PatternAgents/ERA/revisions/Backplane_Reference_R2_0/images/Backplane_Reference_R1_0_top.png

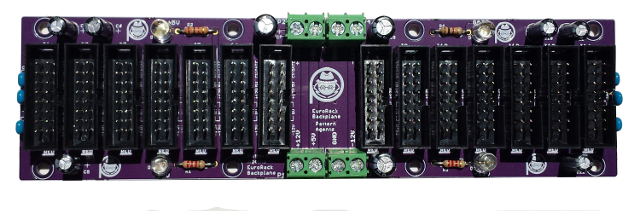
revisions/Backplane_Reference_R2_0/images/Backplane_Reference_R1_0_top.png
