PatternAgents/ERA/revisions/Backplane_Reference_R2_0/images/Backplane_Reference_R2_0_bot.png

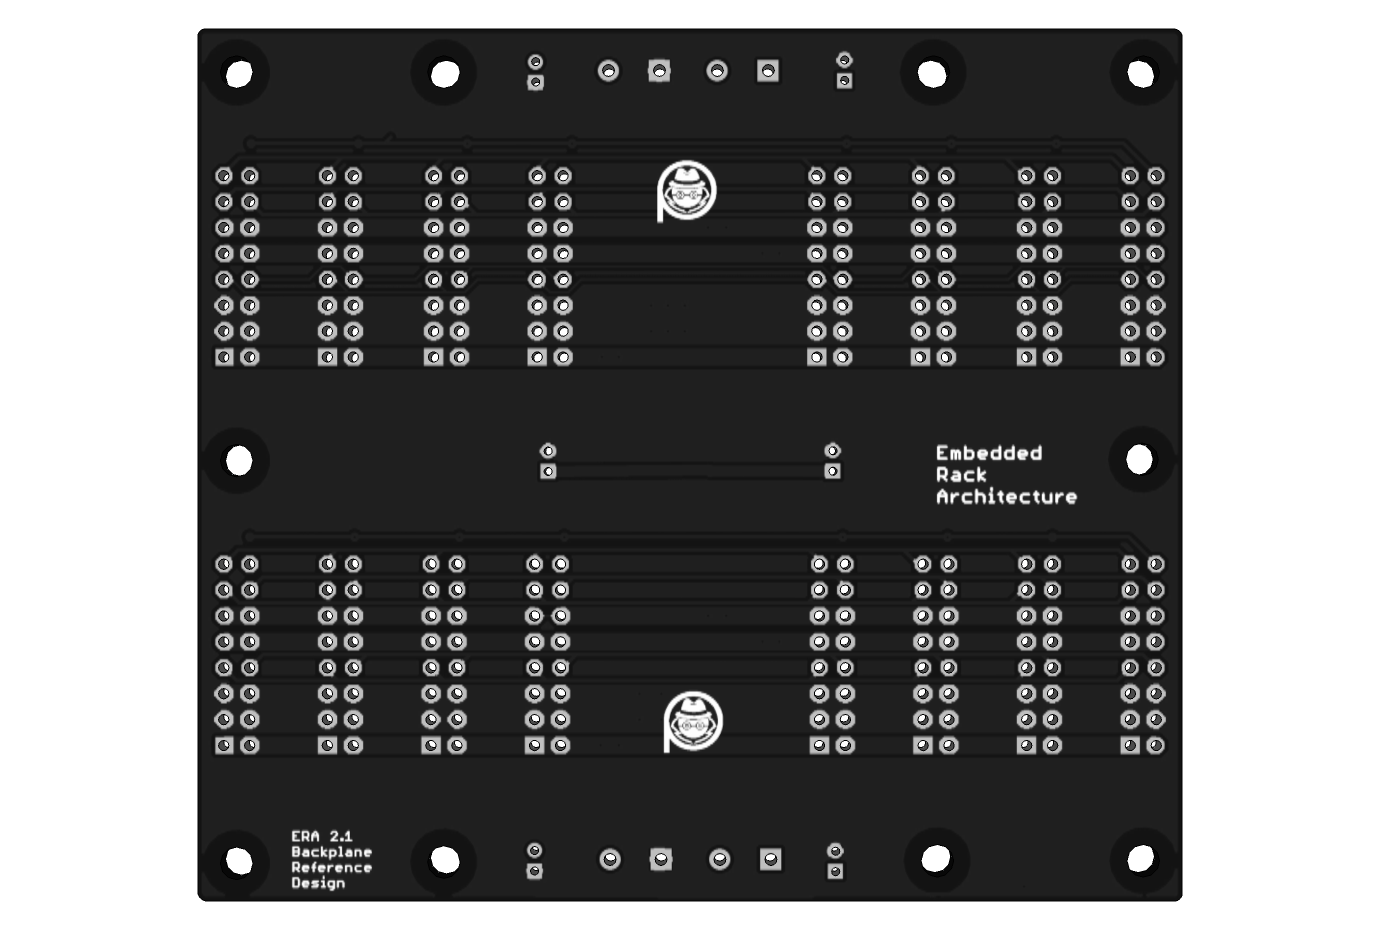
revisions/Backplane_Reference_R2_0/images/Backplane_Reference_R2_0_bot.png
