PatternAgents/ERA/revisions/Backplane_Reference_R2_0/images/Backplane_Reference_R2_0_iso.png

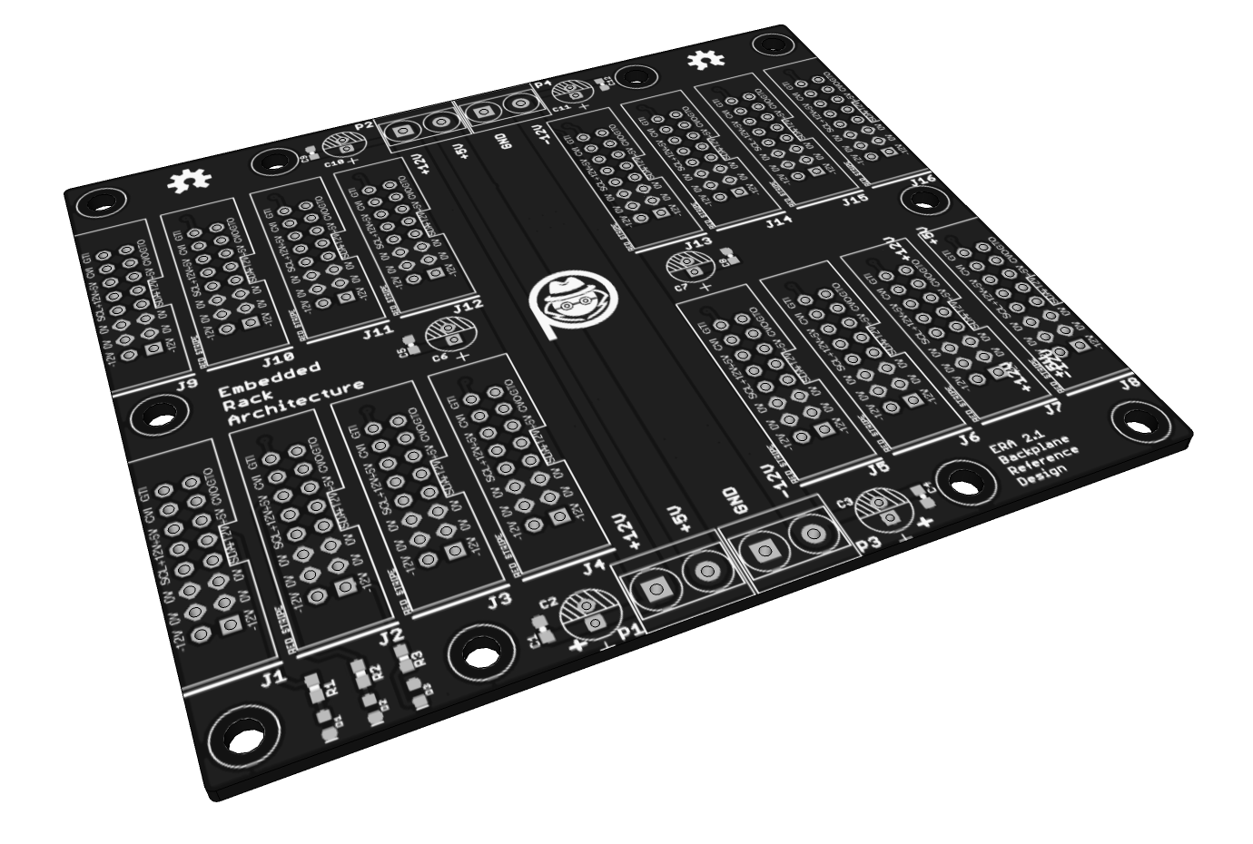
revisions/Backplane_Reference_R2_0/images/Backplane_Reference_R2_0_iso.png
