PatternAgents/ERA/revisions/Module_Templates_1U_PULP/examples/BAM/eagleUp/eagleUp_BAM_SIMPLE_1U_6HP_bottom_silk.png

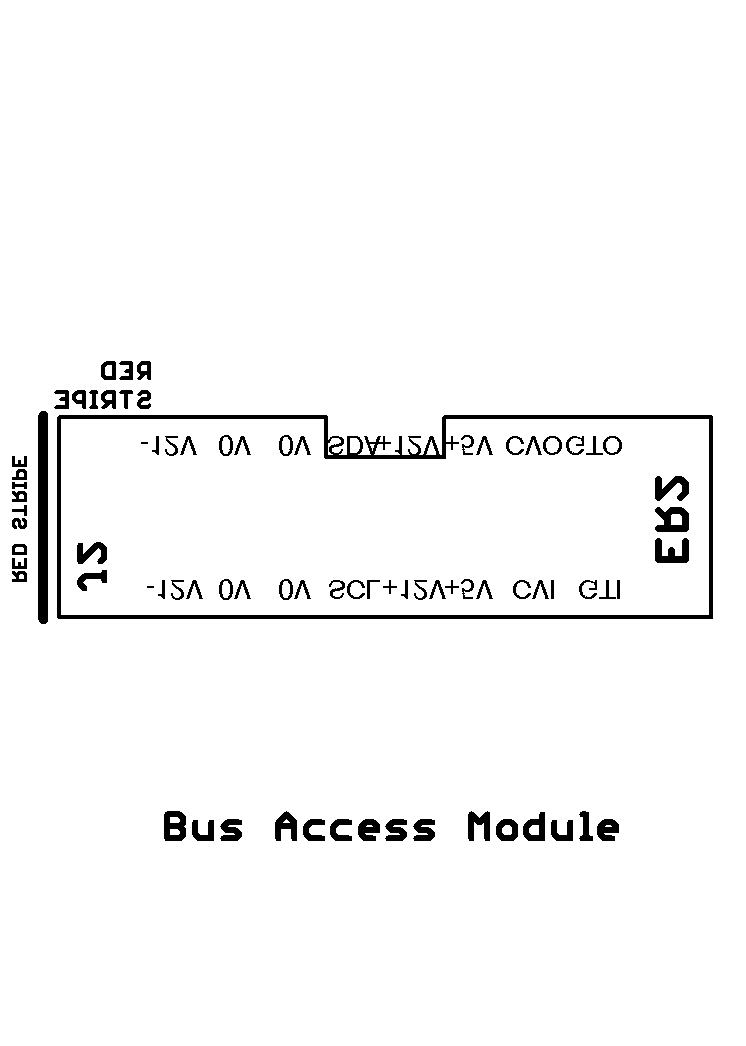
revisions/Module_Templates_1U_PULP/examples/BAM/eagleUp/eagleUp_BAM_SIMPLE_1U_6HP_bottom_silk.png
