PatternAgents/ERA/revisions/Module_Templates_1U_PULP/examples/BUF/eagleUp/eagleUp_BUF_1U_6HP_fpb_bottom.png

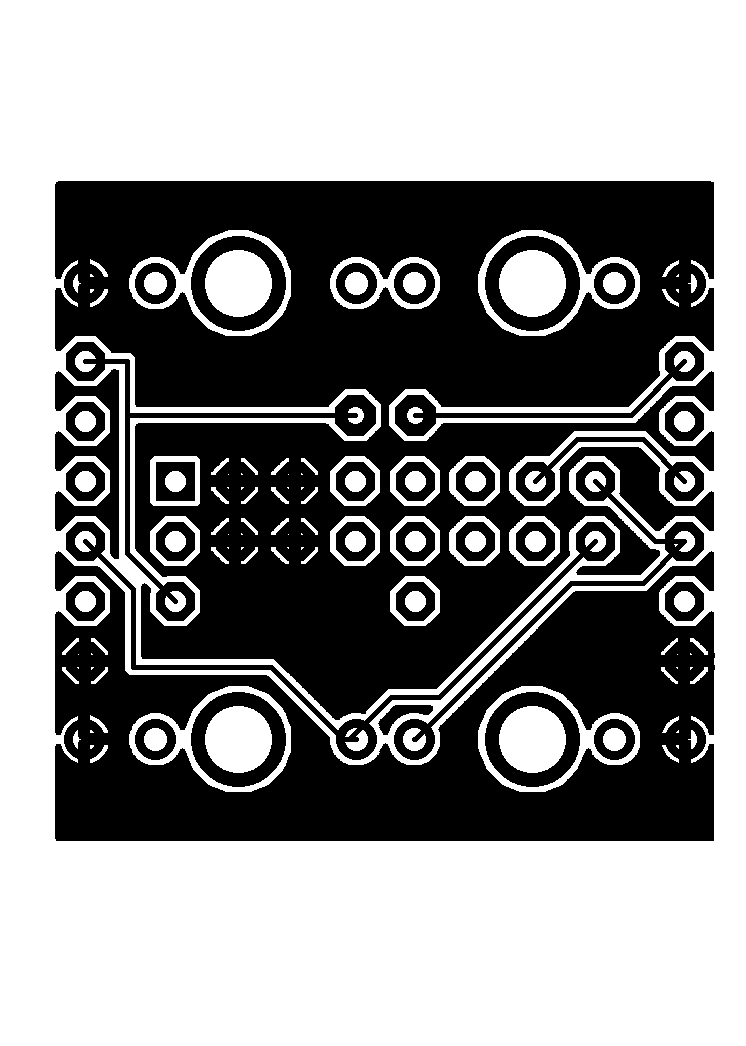
revisions/Module_Templates_1U_PULP/examples/BUF/eagleUp/eagleUp_BUF_1U_6HP_fpb_bottom.png
