PatternAgents/ERA/revisions/Module_Templates_1U_PULP/examples/BUF/eagleUp/eagleUp_BUF_1U_6HP_fpb_top.png

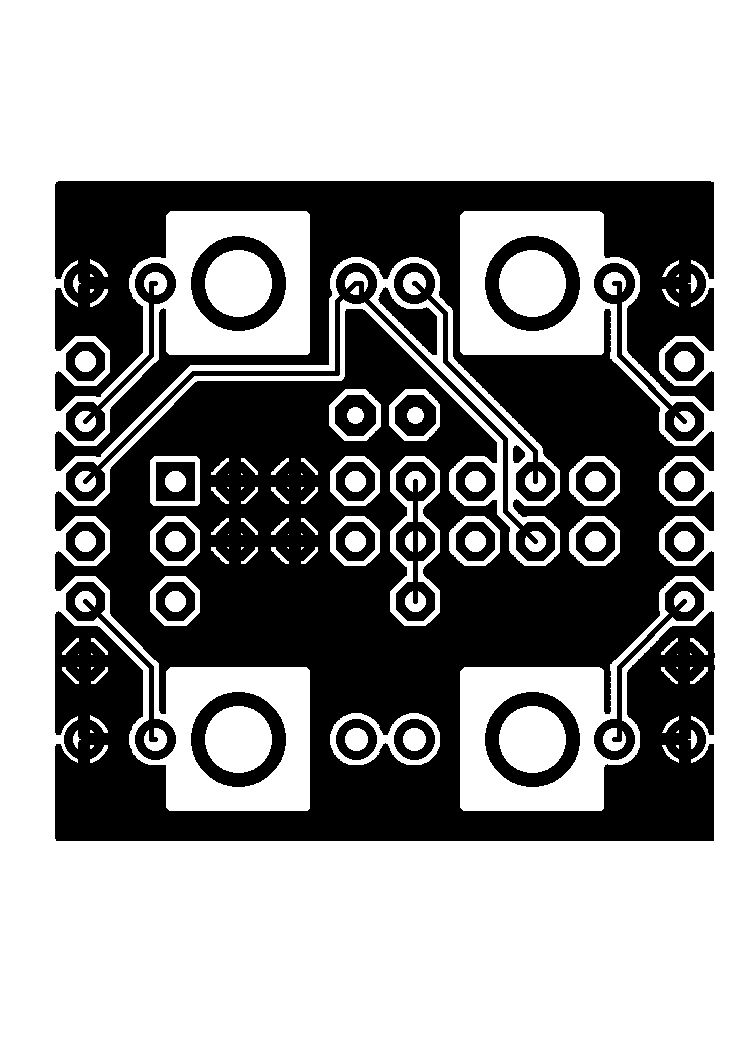
revisions/Module_Templates_1U_PULP/examples/BUF/eagleUp/eagleUp_BUF_1U_6HP_fpb_top.png
