PatternAgents/ERA/revisions/Module_Templates_3U/examples/BAM/eagleUp/eagleUp_BAM_Reference_R2_1_board_bottom.jpg

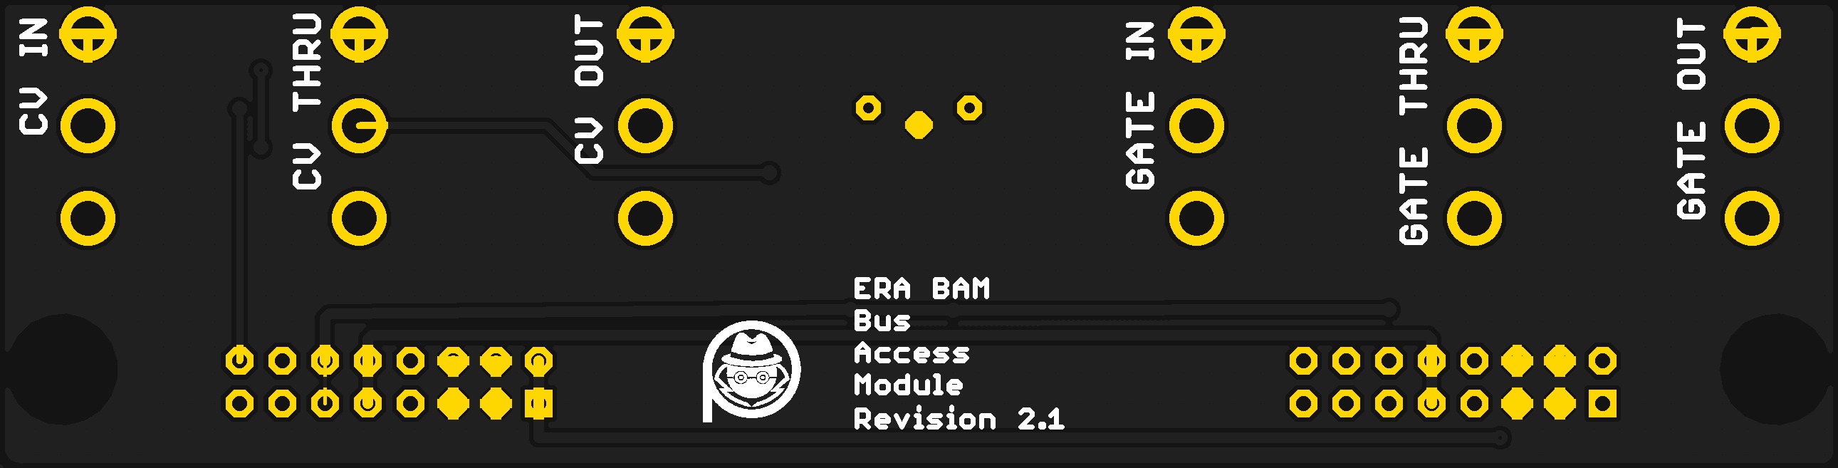
revisions/Module_Templates_3U/examples/BAM/eagleUp/eagleUp_BAM_Reference_R2_1_board_bottom.jpg
