PatternAgents/ERA/revisions/Module_Templates_3U/examples/BAM/images/BAM_iso.png

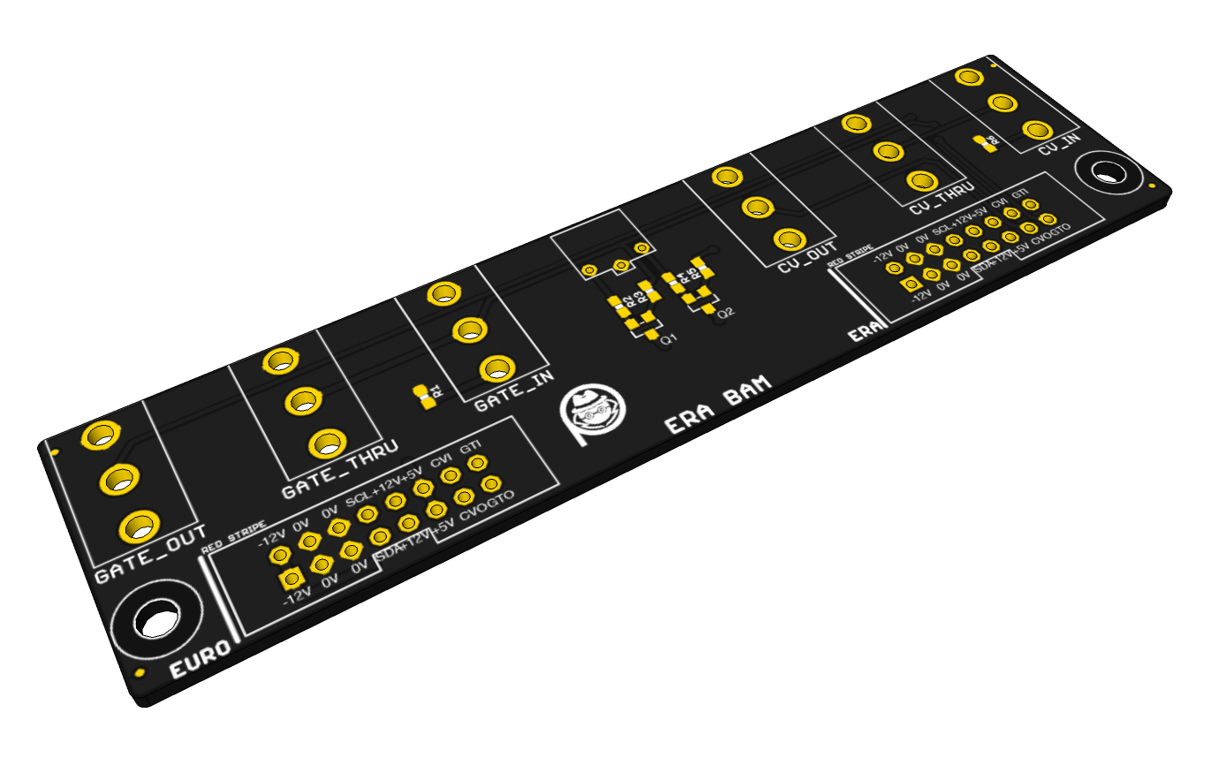
revisions/Module_Templates_3U/examples/BAM/images/BAM_iso.png
