PatternAgents/ERA/revisions/Module_Templates_3U/examples/midi_block/pcb/eagleUp/eagleUp_midi_block_board_bottom.jpg

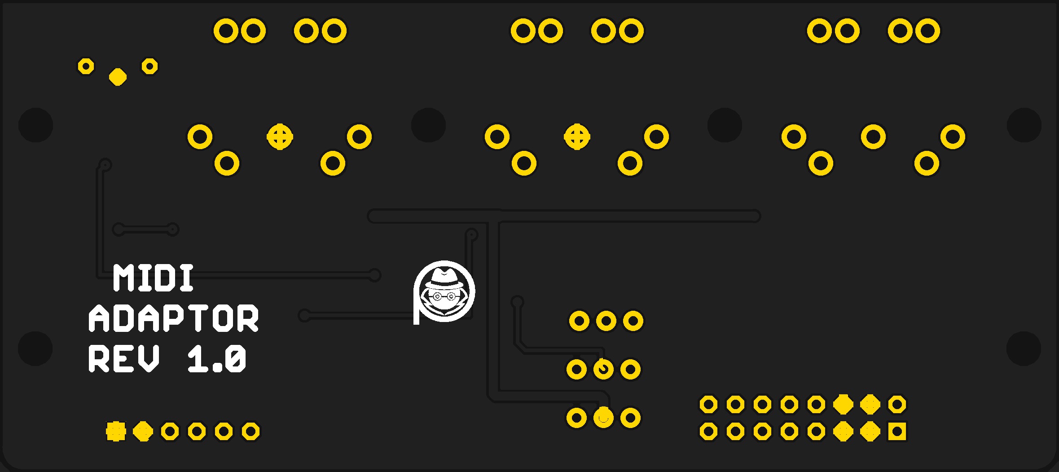
revisions/Module_Templates_3U/examples/midi_block/pcb/eagleUp/eagleUp_midi_block_board_bottom.jpg
