PatternAgents/ERA/revisions/Module_Templates_3U/examples/SwitchMult/eagleUp/eagleUp_SwitchMult_board_bottom.jpg

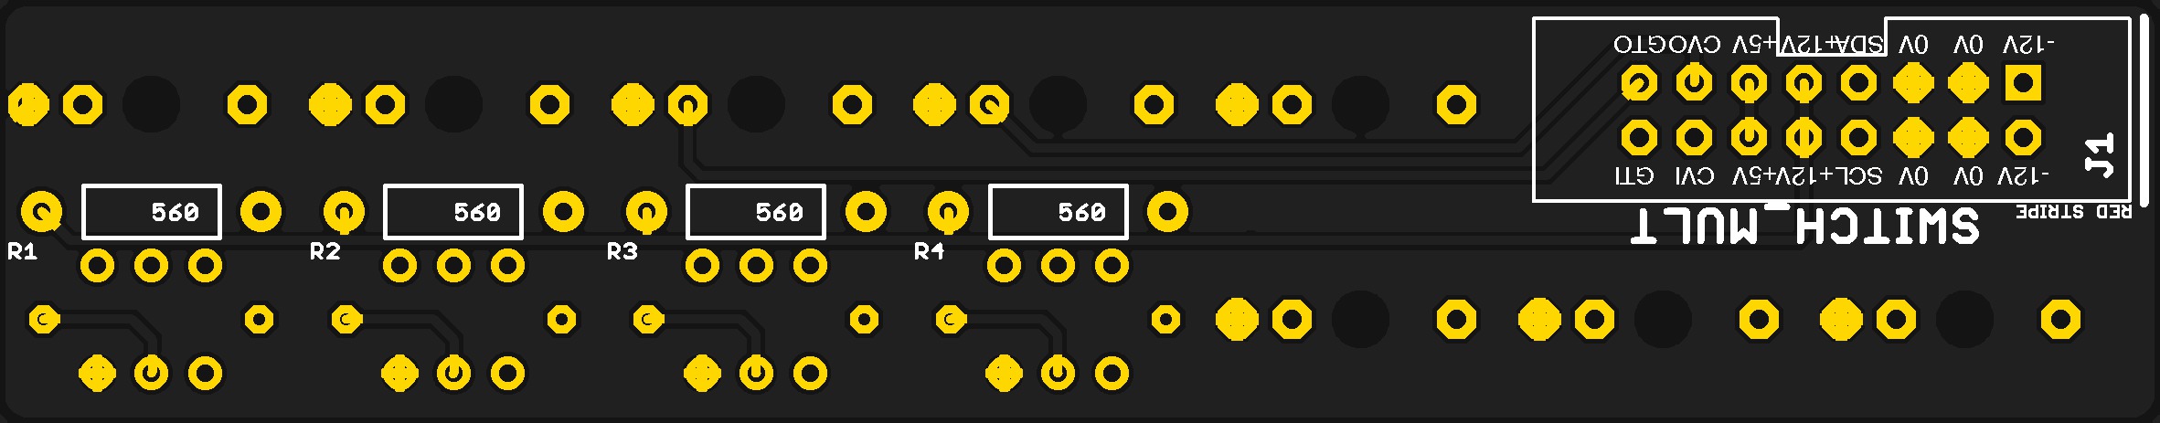
revisions/Module_Templates_3U/examples/SwitchMult/eagleUp/eagleUp_SwitchMult_board_bottom.jpg
