PatternAgents/ERA/revisions/Module_Templates_3U/examples/SwitchMult/eagleUp/eagleUp_SwitchMult_board_top.jpg

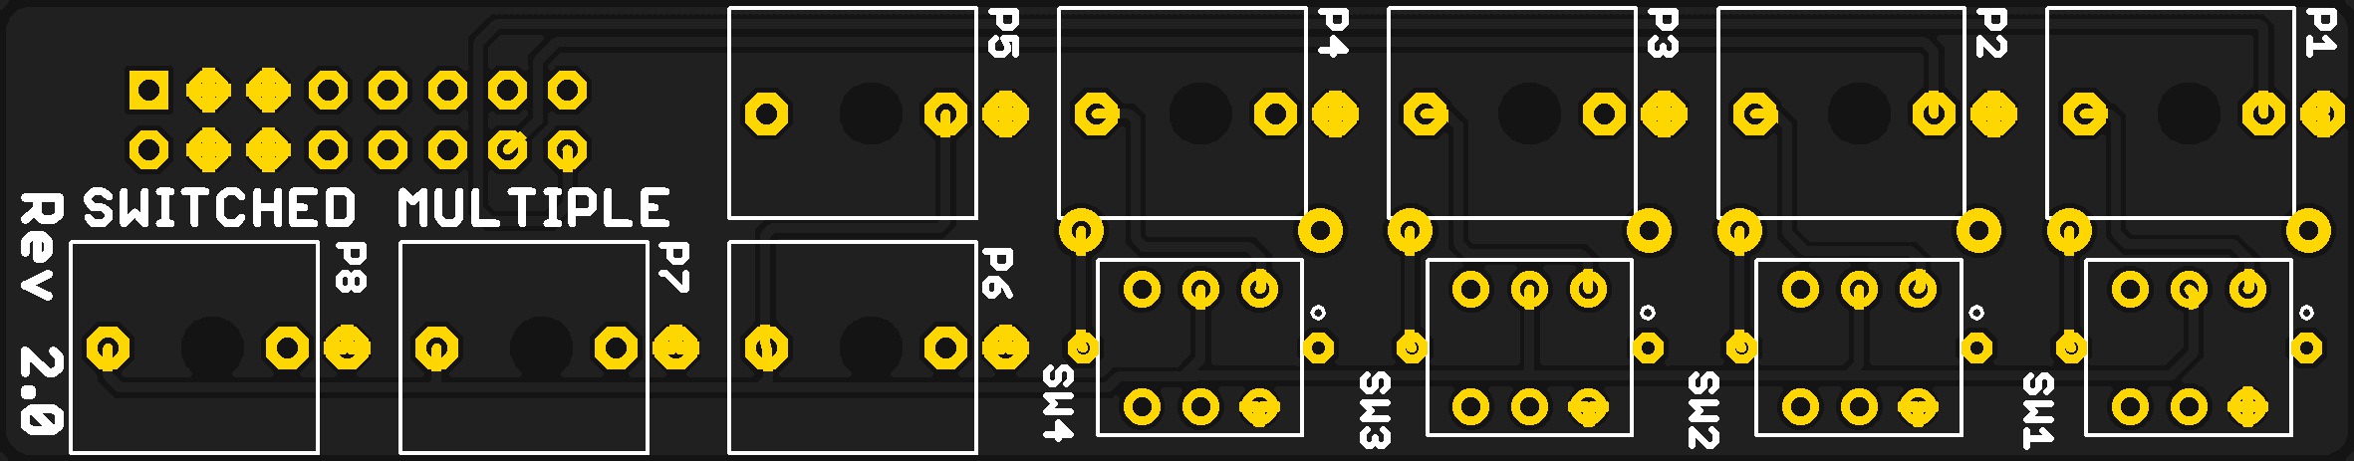
revisions/Module_Templates_3U/examples/SwitchMult/eagleUp/eagleUp_SwitchMult_board_top.jpg
