PatternAgents/ERA/revisions/Module_Templates_3U/examples/SwitchMult/images/SwitchMult_bot.png

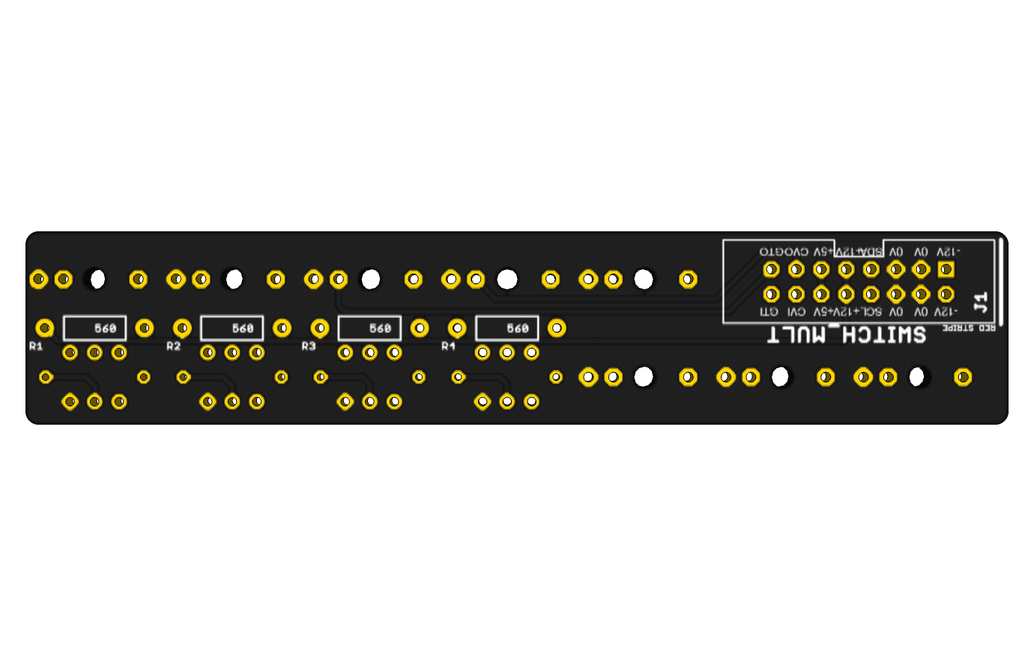
revisions/Module_Templates_3U/examples/SwitchMult/images/SwitchMult_bot.png
