PatternAgents/ERA/revisions/Module_Templates_3U/examples/SwitchMult/images/SwitchMult_panel.png

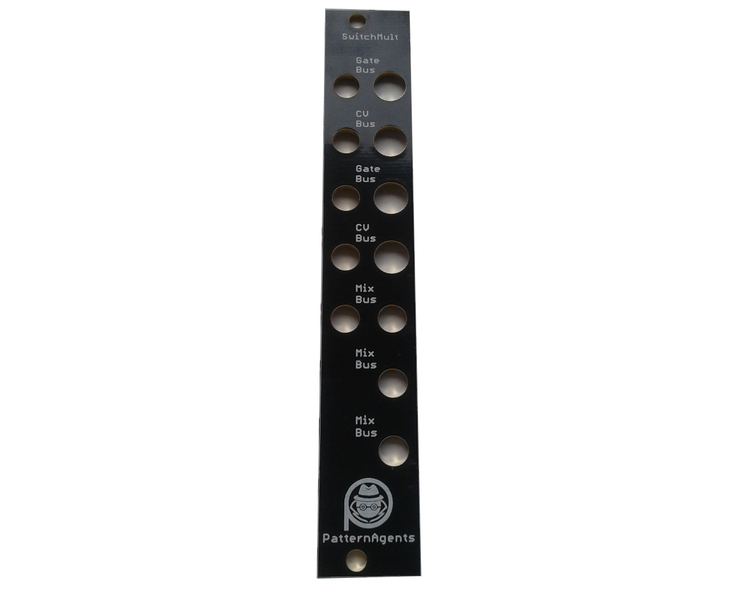
revisions/Module_Templates_3U/examples/SwitchMult/images/SwitchMult_panel.png
