PatternAgents/ERA/revisions/Module_Templates_1U_PULP/examples/BUF/BUF_1U_6HP_fpb.brd

## EAGLE design revisions/Module_Templates_1U_PULP/examples/BUF/BUF_1U_6HP_fpb.brd (2018-01-20)

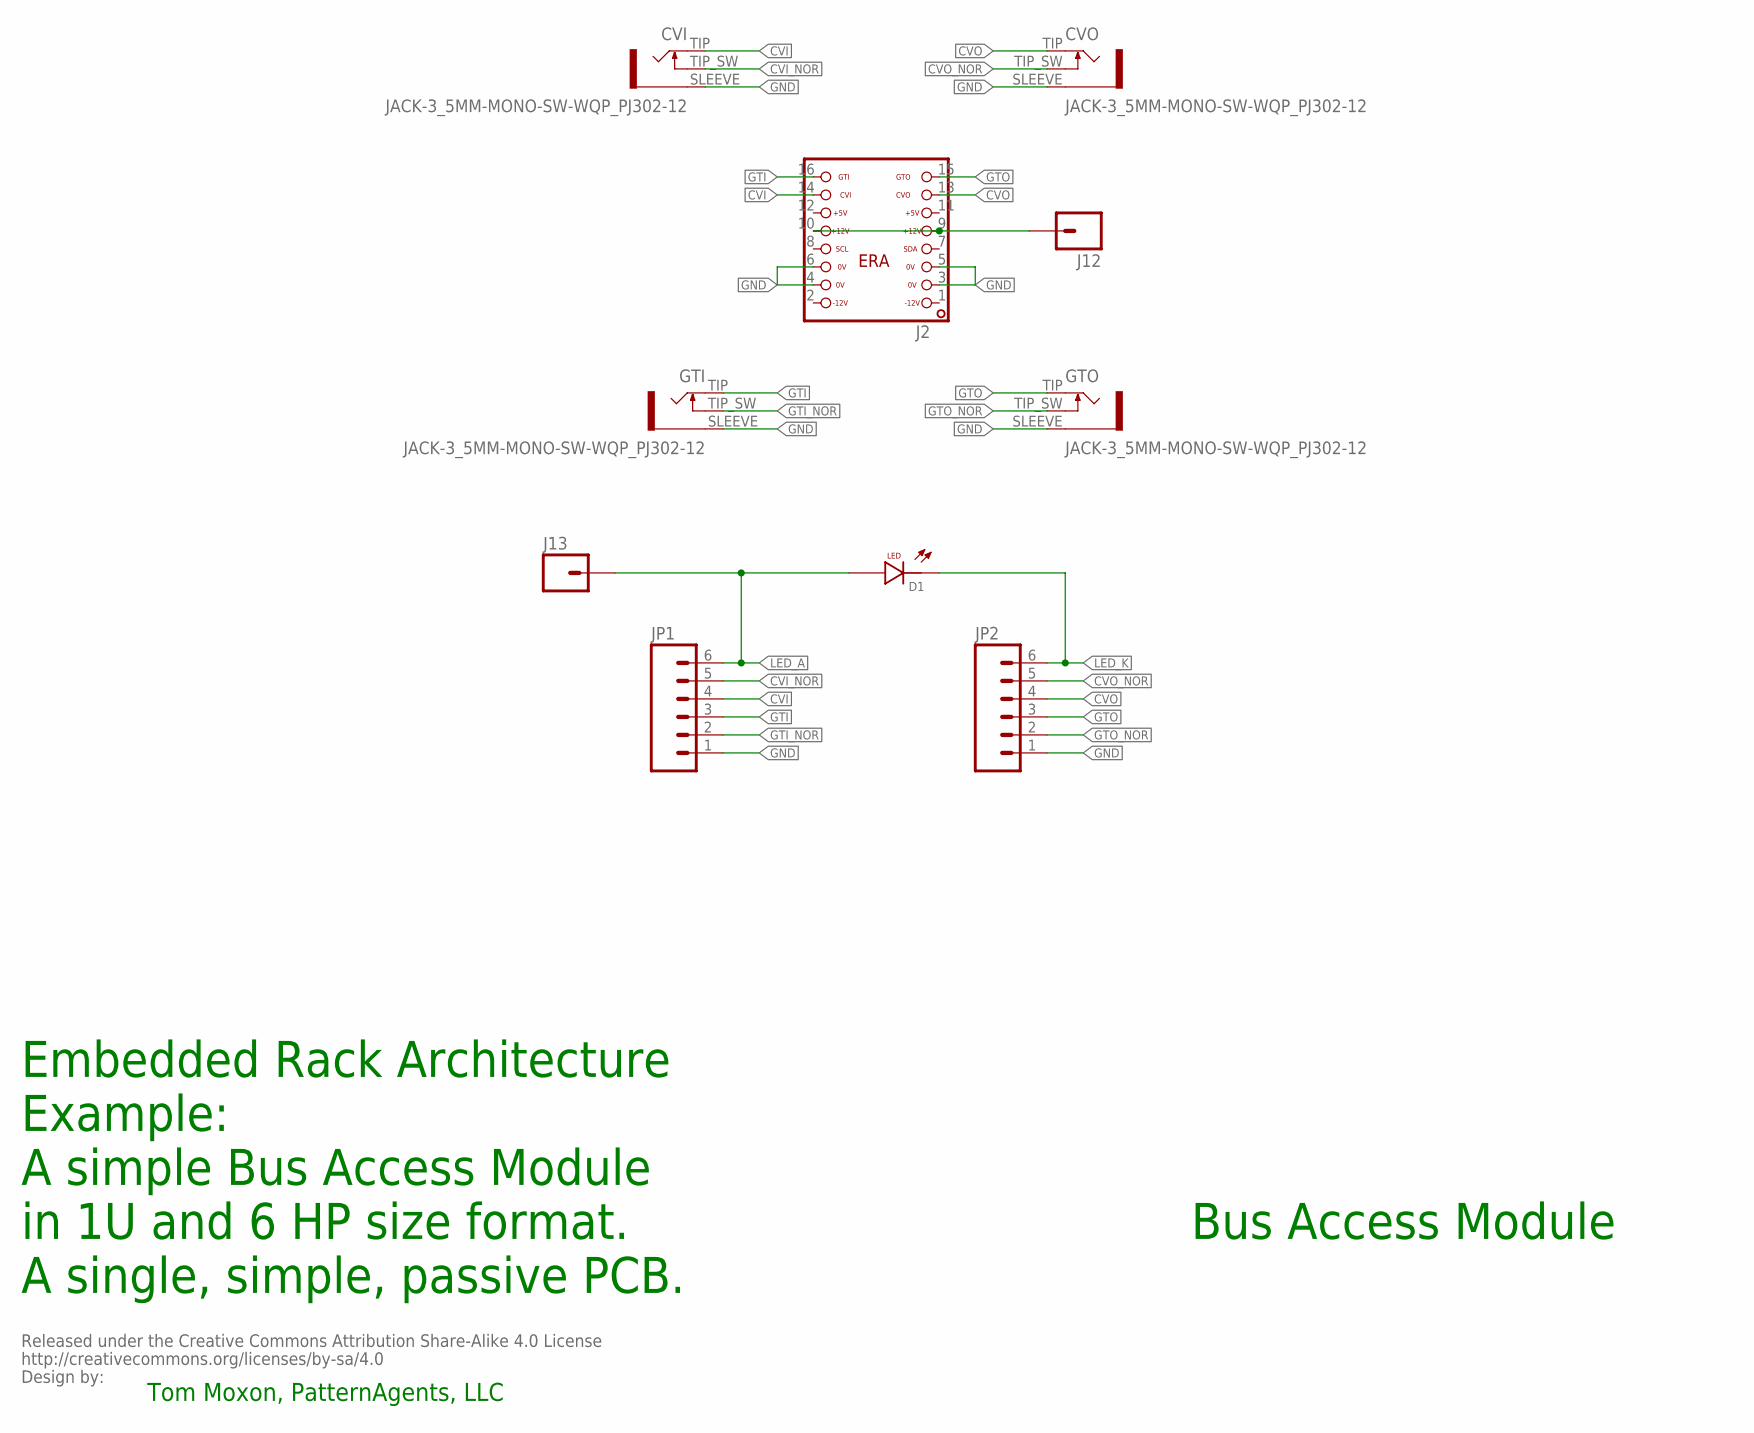
[picture p48: schematic BUF_1U_6HP_fpb.sch]

Parts:
CVI: JACK-3_5MM-MONO-SW-WQP_PJ302-12; WQP_PJ301M-12
CVO: JACK-3_5MM-MONO-SW-WQP_PJ302-12; WQP_PJ301M-12
D1: LED; LED3MM
GTI: JACK-3_5MM-MONO-SW-WQP_PJ302-12; WQP_PJ301M-12
GTO: JACK-3_5MM-MONO-SW-WQP_PJ302-12; WQP_PJ301M-12
J2: ERA-NOSILK
J12, J13: M01PTH; 1X01
JP1, JP2: M06SIP; 1X06
TOMMOXON: BY_CC_SA_TEXTNULL; NULL_SYM

Connections:
CVI: CVI.TIP, J2.14, JP1.4
CVI_NOR: CVI.TIP_SW, JP1.5
CVO: CVO.TIP, J2.13, JP2.4
CVO_NOR: CVO.TIP_SW, JP2.5
GND: CVI.SLEEVE, CVO.SLEEVE, GTI.SLEEVE, GTO.SLEEVE, J2.3, J2.4, J2.5, J2.6, JP1.1, JP2.1
GTI: GTI.TIP, J2.16, JP1.3
GTI_NOR: GTI.TIP_SW, JP1.2
GTO: GTO.TIP, J2.15, JP2.3
GTO_NOR: GTO.TIP_SW, JP2.2
LED_A: D1.A (ANODE), J13.1, JP1.6
LED_K: D1.K (CATHODE), JP2.6
unnamed: J2.9, J2.10, J12.1

Notes on the sheet:
Bus Access Module
Embedded Rack Architecture Example: A simple Bus Access Module in 1U and 6 HP size format. A single, simple, passive PCB.
Tom Moxon, PatternAgents, LLC

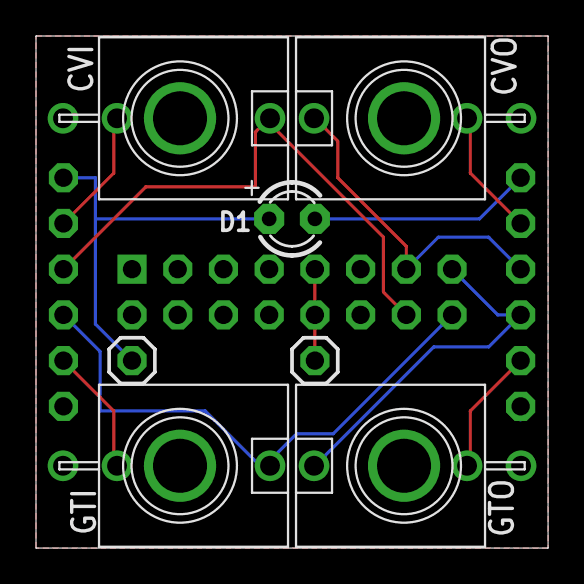
[picture p49: board BUF_1U_6HP_fpb.brd from above]

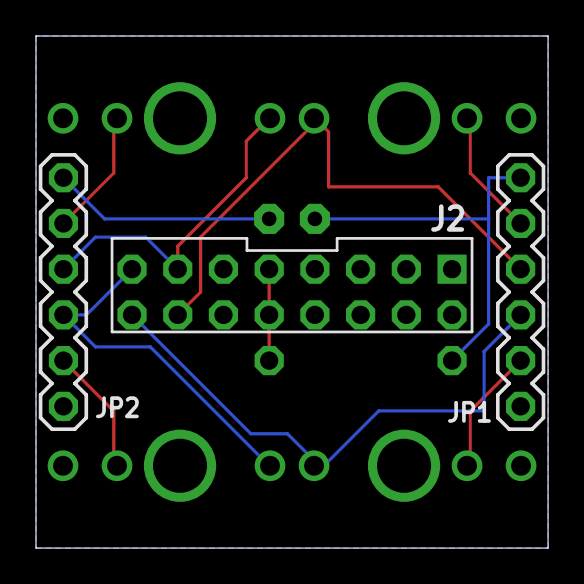
[picture p50: board BUF_1U_6HP_fpb.brd from below]

Board: 2 copper layers, 28.4 x 28.4 mm, 11 parts (3 on the bottom side), 12 nets.
