PatternAgents/ERA/revisions/Module_Templates_3U/examples/BAM/BAM_Reference_R2_1.brd

## EAGLE design revisions/Module_Templates_3U/examples/BAM/BAM_Reference_R2_1.brd (2018-04-10)

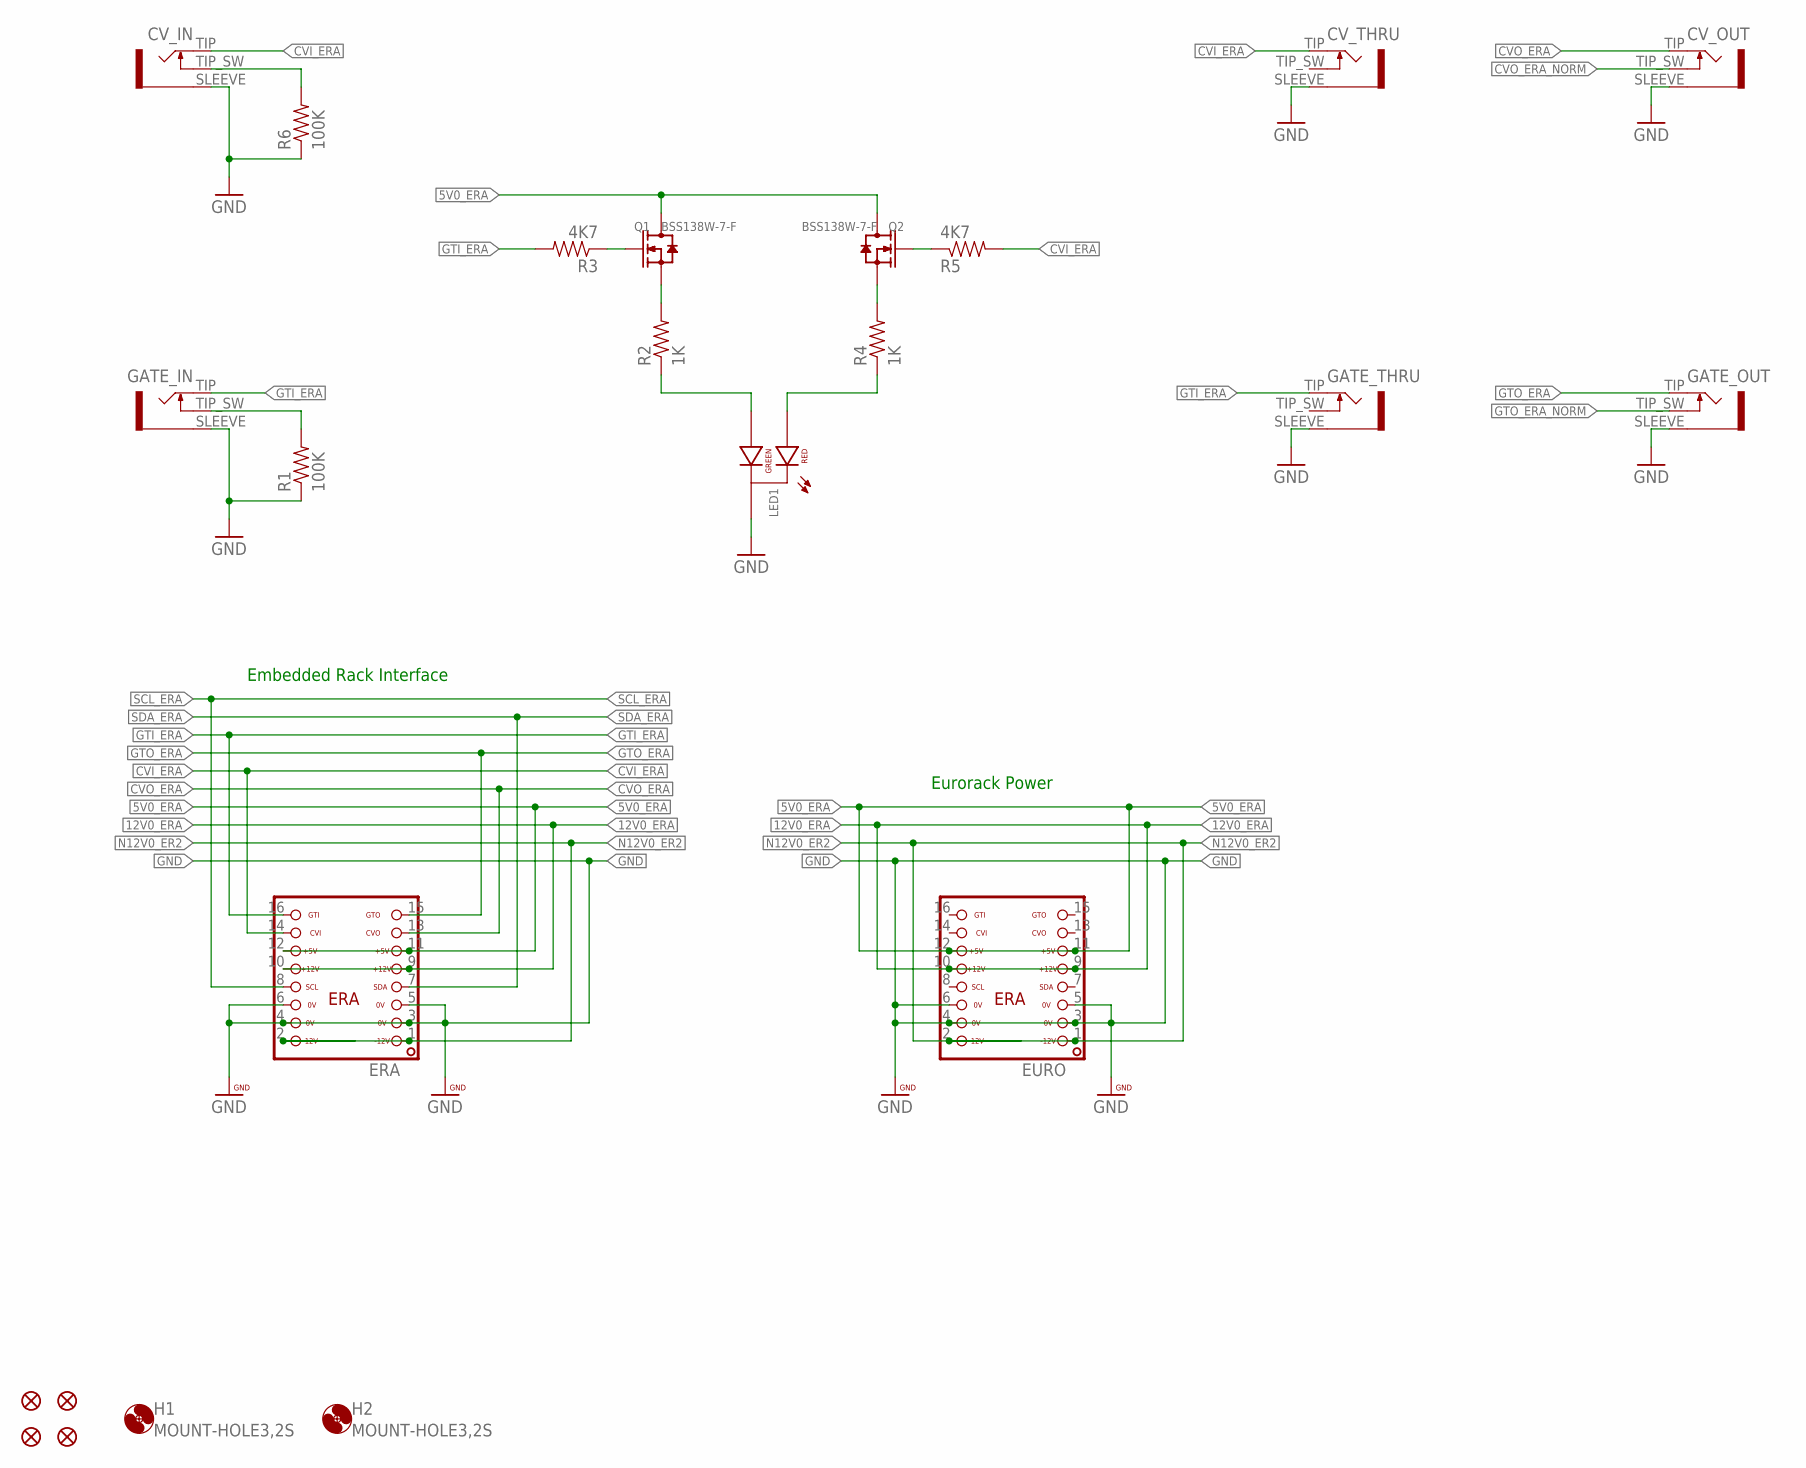
[picture p55: schematic BAM_Reference_R2_1.sch]

Parts:
CV_IN: JACK-3_5MM-MONO-SW-MJ_3502; MJ-3502
CV_OUT: JACK-3_5MM-MONO-SW-MJ_3502; MJ-3502
CV_THRU: JACK-3_5MM-MONO-SW-MJ_3502; MJ-3502
ERA: ERA-SHROUD; ERA
EURO: ERA-SHROUD; ERA
FID1, FID2, FID3, FID4: FIDUCIALUFIDUCIAL; MICRO-FIDUCIAL
GATE_IN: JACK-3_5MM-MONO-SW-MJ_3502; MJ-3502
GATE_OUT: JACK-3_5MM-MONO-SW-MJ_3502; MJ-3502
GATE_THRU: JACK-3_5MM-MONO-SW-MJ_3502; MJ-3502
H1, H2: MOUNT-HOLE3,2S; 3,2,SMALL
LED1: LED-RG-CC-PTH-G18500; LED-RG-PANEL
Q1, Q2: BSS138W-7-F; SOT-23
R1, R6: 100K; 0603-RES
R2, R4: 1K; 0603-RES
R3, R5: 4K7; 0603-RES

Connections:
5V0_ERA: ERA.11, ERA.12, EURO.11, EURO.12, Q1.3 (D), Q2.3 (D)
12V0_ERA: ERA.9, ERA.10, EURO.9, EURO.10
CVI_ERA: CV_IN.TIP, CV_THRU.TIP, ERA.14, R5.2
CVO_ERA: CV_OUT.TIP, ERA.13
CVO_ERA_NORM: CV_OUT.TIP_SW
GND: CV_IN.SLEEVE, CV_OUT.SLEEVE, CV_THRU.SLEEVE, ERA.3, ERA.4, ERA.5, ERA.6, EURO.3, EURO.4, EURO.5, EURO.6, GATE_IN.SLEEVE, GATE_OUT.SLEEVE, GATE_THRU.SLEEVE, LED1.CC (CATHODE), R1.1, R6.1
GTI_ERA: ERA.16, GATE_IN.TIP, GATE_THRU.TIP, R3.2
GTO_ERA: ERA.15, GATE_OUT.TIP
GTO_ERA_NORM: GATE_OUT.TIP_SW
N12V0_ER2: ERA.1, ERA.2, EURO.1, EURO.2
unnamed: LED1.GREEN (GREEN_CATHODE), R2.1
unnamed: LED1.RED (RED_CATHODE), R4.1
unnamed: Q1.1 (G), R3.1
unnamed: Q2.2 (S), R4.2
unnamed: Q2.1 (G), R5.1
unnamed: Q1.2 (S), R2.2
unnamed: CV_IN.TIP_SW, R6.2
unnamed: GATE_IN.TIP_SW, R1.2
SCL_ERA: ERA.8
SDA_ERA: ERA.7

Notes on the sheet:
Embedded Rack Interface
Eurorack Power

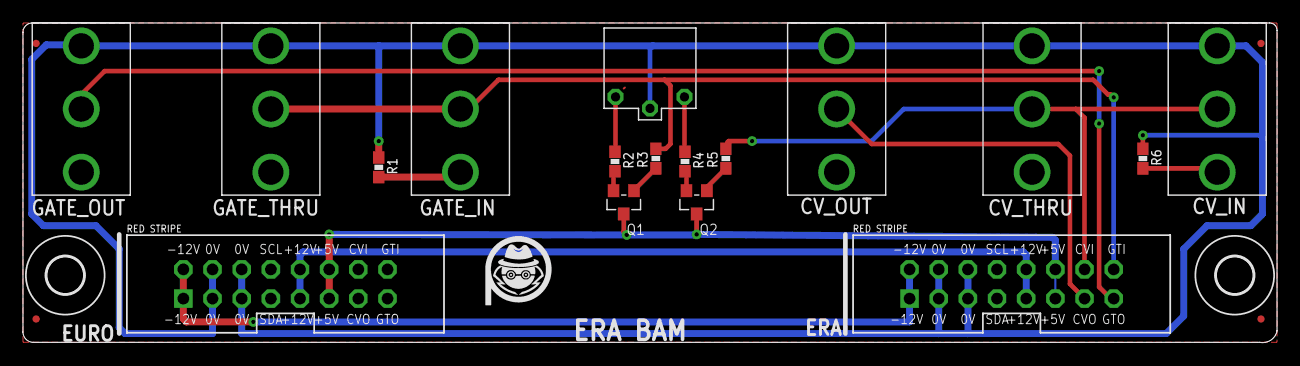
[picture p56: board BAM_Reference_R2_1.brd from above]

Board: 2 copper layers, 109.2 x 27.8 mm, 26 parts (1 on the bottom side), 16 nets.

Other parts of the board:
U$1, U$2: PA_LOGO_SYMMED; PA_LOGO_AGENT_MED_SYM
U$48: BY_CC_SA_TEXTTEXT; BY_CC_SA_TEXT
