PatternAgents/ERA/revisions/Module_Templates_3U/examples/midi_block/pcb/midi_block.brd

## EAGLE design revisions/Module_Templates_3U/examples/midi_block/pcb/midi_block.brd (2018-04-10)

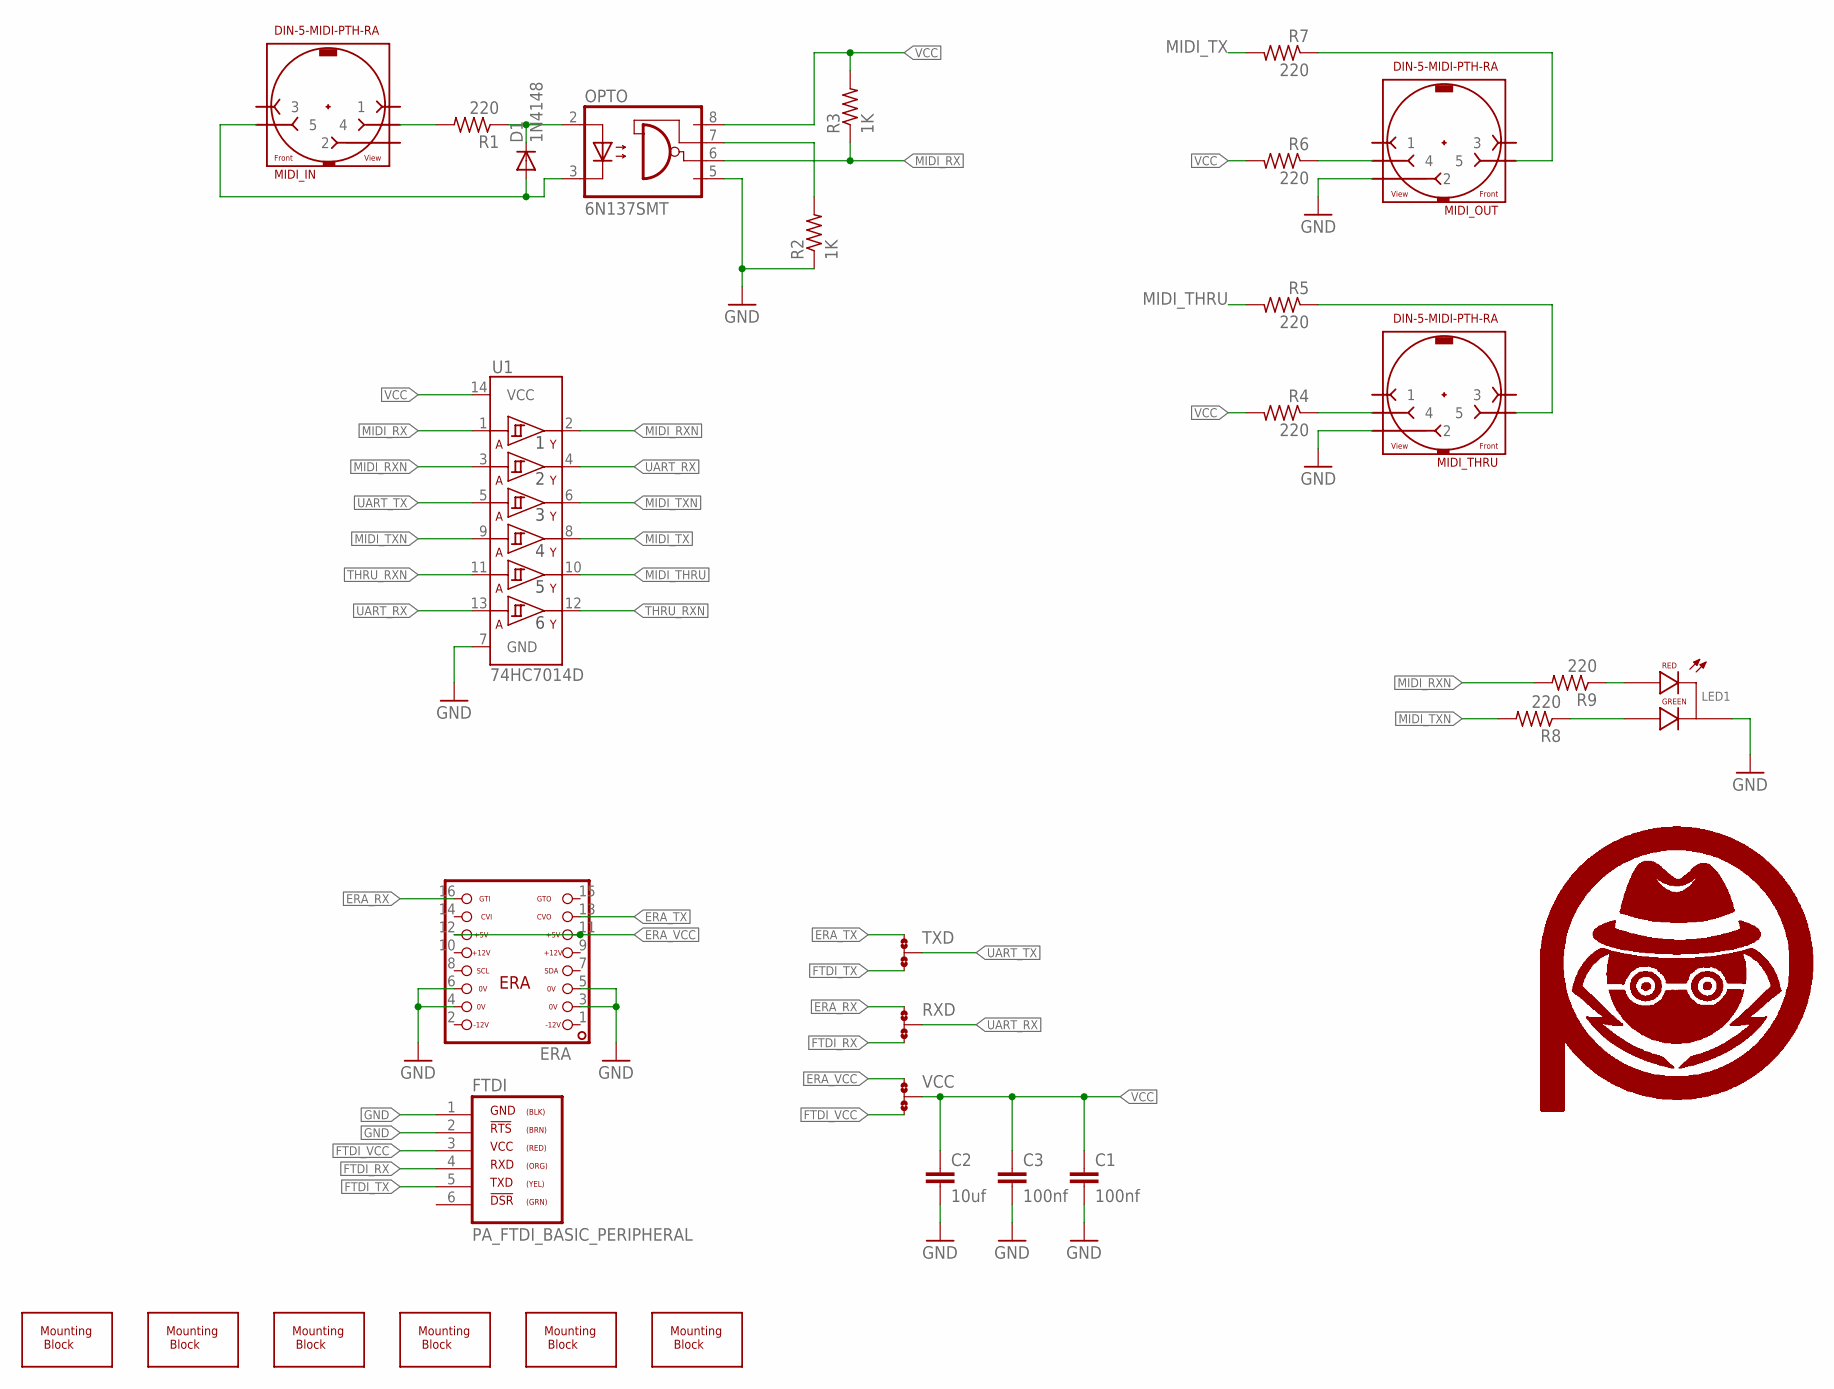
[picture p57: schematic midi_block.sch]

Parts:
C1, C3: 100nf; 0603-CAP
C2: 10uf; 0603-CAP
D1: 1N4148; SOD323-W
ERA: ERA-SHROUD; ERA
FTDI: PA_FTDI_BASIC_PERIPHERAL; PA_PMOD_SIL_MALE
LED1: LED-RG-CC-PTH-G18500; LED-RG-PANEL
MIDI_IN: DIN-5-MIDI-PTH-RA; DIN-5-PTH-RA-SUPPORT
MIDI_OUT: DIN-5-MIDI-PTH-RA; DIN-5-PTH-RA-SUPPORT
MIDI_THRU: DIN-5-MIDI-PTH-RA; DIN-5-PTH-RA-SUPPORT
OPTO: 6N137SMT; DIL8-SMD
R1, R4, R5, R6, R7, R8, R9: 220; R0603
R2, R3: 1K; R0603
RXD: JMP-3-NO-PTH; JMP-3-NO-PTH-2.54
TXD: JMP-3-NO-PTH; JMP-3-NO-PTH-2.54
U1: 74HC7014D; SOIC-14
U$1, U$2, U$3, U$4, U$7, U$8: PCB-MB-SIDE; PCB-MB-01-SIDE
U$5, U$6: PA_LOGO_SYMMED; PA_LOGO_AGENT_MED_SYM
VCC: JMP-3-NO-PTH; JMP-3-NO-PTH-2.54

Connections:
CL_IN: MIDI_IN.4, R1.2
ERA_RX: ERA.16, RXD.1
ERA_TX: ERA.13, TXD.1
ERA_VCC: ERA.11, ERA.12, VCC.1
FTDI_RX: FTDI.4, RXD.3
FTDI_TX: FTDI.5, TXD.3
FTDI_VCC: FTDI.3, VCC.3
GND: C1.2, C2.2, C3.2, ERA.3, ERA.4, ERA.5, ERA.6, FTDI.1, FTDI.2, LED1.CC (CATHODE), MIDI_OUT.2, MIDI_THRU.2, OPTO.5 (GND), R2.1, U1.7 (GND)
MIDI_IN: D1.A, MIDI_IN.5, OPTO.3 (C)
MIDI_OUT: MIDI_OUT.5, R7.1
MIDI_OUT1: MIDI_THRU.5, R5.1
MIDI_RX: OPTO.6 (VO), R3.1, U1.1 (1A)
MIDI_RXN: R9.2, U1.2 (1Y), U1.3 (2A)
MIDI_THRU: R5.2, U1.10 (5Y)
MIDI_TX: R7.2, U1.8 (4Y)
MIDI_TXN: R8.2, U1.6 (3Y), U1.9 (4A)
unnamed: LED1.RED (RED_CATHODE), R9.1
unnamed: LED1.GREEN (GREEN_CATHODE), R8.1
unnamed: MIDI_THRU.4, R4.1
unnamed: OPTO.7 (VE), R2.2
unnamed: D1.C, OPTO.2 (A), R1.1
unnamed: MIDI_OUT.4, R6.1
THRU_RXN: U1.11 (5A), U1.12 (6Y)
UART_RX: RXD.2, U1.4 (2Y), U1.13 (6A)
UART_TX: TXD.2, U1.5 (3A)
VCC: C1.1, C2.1, C3.1, OPTO.8 (VCC), R3.2, R4.2, R6.2, U1.14 (VCC), VCC.2

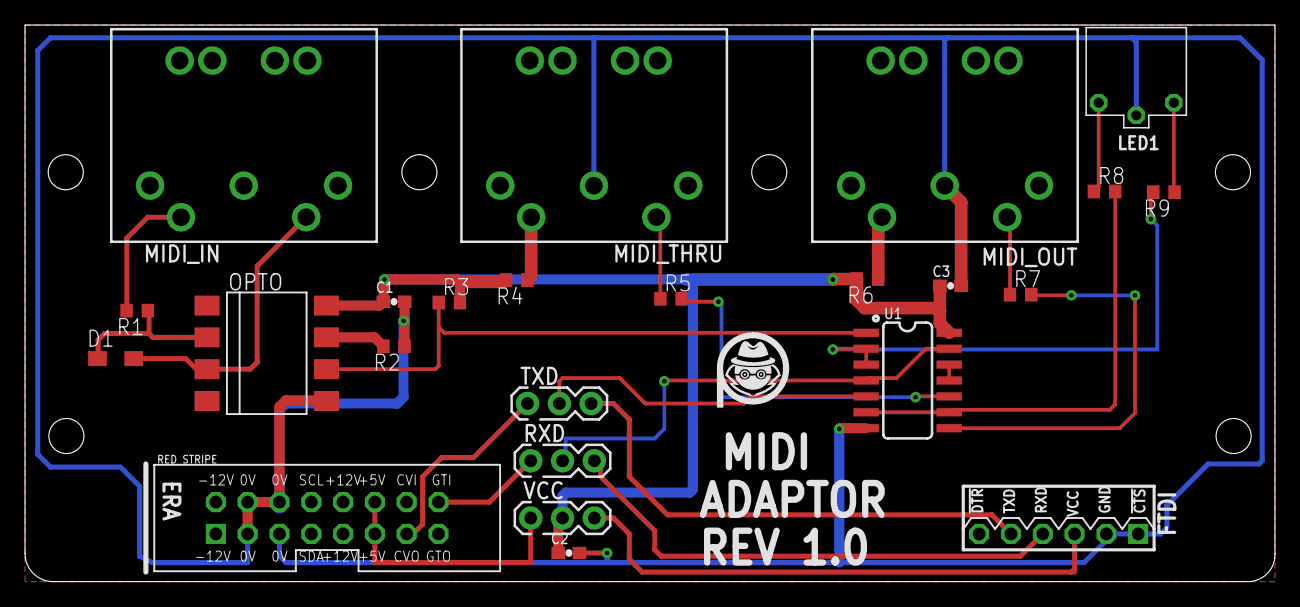
[picture p58: board midi_block.brd from above]

Board: 2 copper layers, 99.8 x 44.5 mm, 32 parts (1 on the bottom side), 26 nets.
